LirokWid/ESE_BMMPE_chat_souris/FINAL_CODE/FINAL_CODE_TAG_ROBOT/Drivers/MPU6050/mpu6050_driver.h

/*
 * mpu6050.h
 *
 *  Created on: Nov 13, 2019
 *      Author: Bulanov Konstantin
 */

#ifndef INC_GY521_H_
#define INC_GY521_H_

#include <stdint.h>
#include <main.h>
#include <math.h>

#define RAD_TO_DEG 57.295779513082320876798154814105

#define WHO_AM_I_REG 0x75
#define PWR_MGMT_1_REG 0x6B
#define SMPLRT_DIV_REG 0x19
#define ACCEL_CONFIG_REG 0x1C
#define ACCEL_XOUT_H_REG 0x3B
#define TEMP_OUT_H_REG 0x41
#define GYRO_CONFIG_REG 0x1B
#define GYRO_XOUT_H_REG 0x43

#define MPU6050_ADDR 0xD0


// MPU6050 structure
typedef struct
{

    int16_t Accel_X_RAW;
    int16_t Accel_Y_RAW;
    int16_t Accel_Z_RAW;
    double Ax;
    double Ay;
    double Az;

    int16_t Gyro_X_RAW;
    int16_t Gyro_Y_RAW;
    int16_t Gyro_Z_RAW;
    double Gx;
    double Gy;
    double Gz;

    float Temperature;

    double KalmanAngleX;
    double KalmanAngleY;
} MPU6050_t;

// Kalman structure
typedef struct
{
    double Q_angle;
    double Q_bias;
    double R_measure;
    double angle;
    double bias;
    double P[2][2];
} Kalman_t;

uint8_t MPU6050_Init(I2C_HandleTypeDef *I2Cx);
void MPU6050_Read_Accel(I2C_HandleTypeDef *I2Cx, MPU6050_t *DataStruct);
void MPU6050_Read_Gyro(I2C_HandleTypeDef *I2Cx, MPU6050_t *DataStruct);
void MPU6050_Read_Temp(I2C_HandleTypeDef *I2Cx, MPU6050_t *DataStruct);
void MPU6050_Read_All(I2C_HandleTypeDef *I2Cx, MPU6050_t *DataStruct);
double Kalman_getAngle(Kalman_t *Kalman, double newAngle, double newRate, double dt);

#endif /* INC_GY521_H_ */
