LirokWid/ESE_BMMPE_chat_souris/FINAL_CODE/FINAL_CODE_TAG_ROBOT/Drivers/MPU6050/mpu6050_task.h

#ifndef TASK_MPU6050
#define TASK_MPU6050

#include "cmsis_os.h"
#include "projdefs.h"
#include <stdio.h>
#include "main.h"
#include "i2c.h"
#include "mpu6050_driver.h"

int Init_mpu6050(int priority,I2C_HandleTypeDef *MPU_i2c_handle_param);
void Mpu6050_Task(void *pvParameters);

#endif
